McMornan/ESP32-Serial-Monitor/20230205_203610.jpg

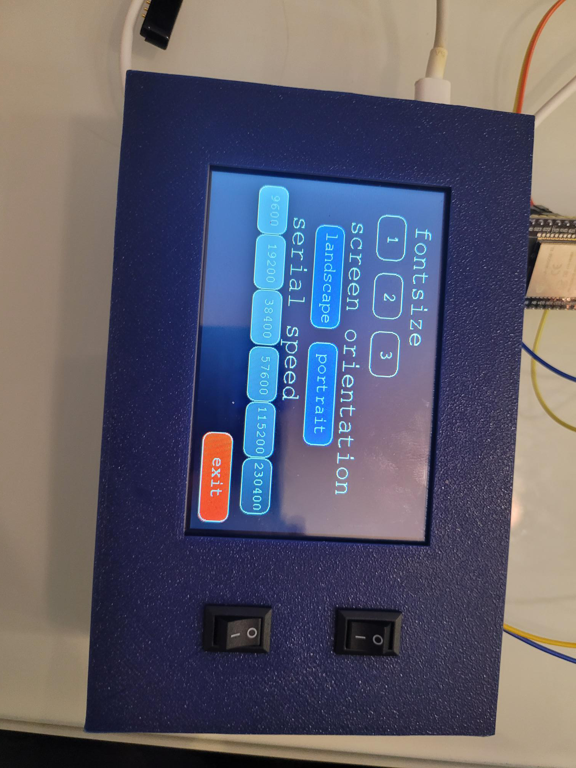
20230205_203610.jpg
