McMornan/ESP32-Serial-Monitor/20230205_203626.jpg

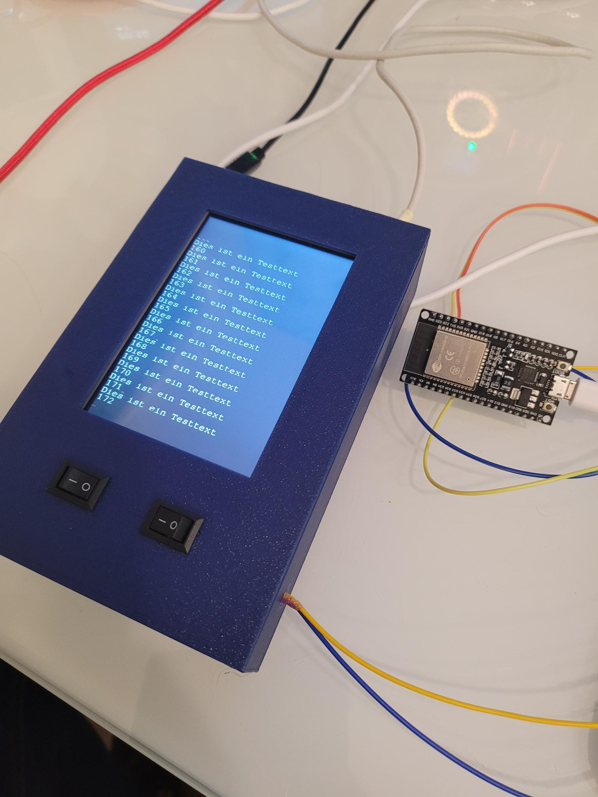
20230205_203626.jpg
